madworm/MBI5030_starter-board/SOP24/gerber_files/PNGs/MBI5030-SOP24_starter-board-B_Cu.gbl.png

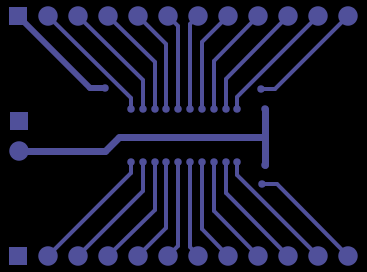
SOP24/gerber_files/PNGs/MBI5030-SOP24_starter-board-B_Cu.gbl.png
