madworm/MBI5030_starter-board/SOP24/gerber_files/PNGs/MBI5030-SOP24_starter-board-Cmts_User.gbr.png

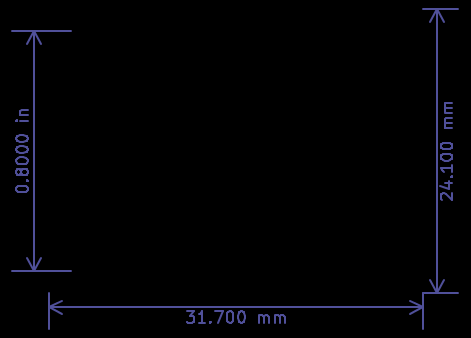
SOP24/gerber_files/PNGs/MBI5030-SOP24_starter-board-Cmts_User.gbr.png
