madworm/MBI5030_starter-board/SOP24/gerber_files/PNGs/MBI5030-SOP24_starter-board-F_SilkS.gto.png

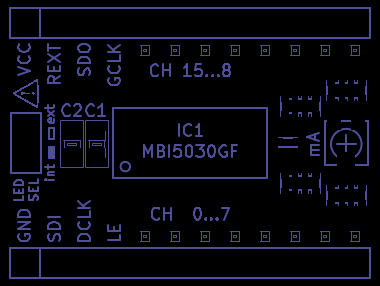
SOP24/gerber_files/PNGs/MBI5030-SOP24_starter-board-F_SilkS.gto.png
